Natologic/plasticTravelPad/img/IMG_3074.JPG

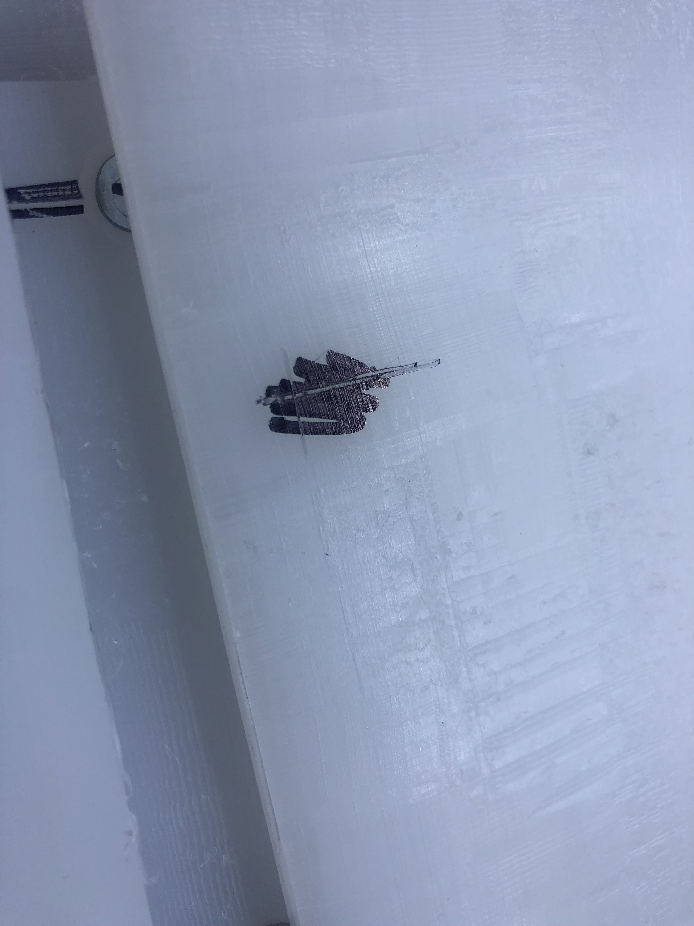
img/IMG_3074.JPG
